jrha/2550N/src/jubilee.sch

## KiCad design src/jubilee.sch (2017-06-12)

Schematic: jubilee.sch

Parts:
C1: 0.047uF
C2, C4, C10, C21, C22, C23: 0.1uF
C3: 0.68uF
C5, C20: 47pF
C6: 0.0047uF
C7: 0.01uF
C8, C11, C18, C26, C30, C31: 50uF 500V
C9, C17: 0.001uF
C12: 220pF
C13, C14: 470pF
C15, C33, C34: 10uF
C16, C19, C24, C25: 0.022uF
C27: 0.0022uF
C28: 22uF
C29: 470uF
C32: 0.002uF
C35: 0.033uF
D1, D2, D3, D4, D6, D7, D9, D11, D12, D13, D14, D15: 1N4007
D5, D8: Red LED 1.8Vf 20mA
D10: LED
F1: 2A SloBlo
F2: 500mA
J1: Input
J2: FX Recv
J3: FX Send
J4: Footswitch
J5, J6: Speaker
JP1, JP2: JUMPER
K1: RELAY_DPDT
K2: Mains
L1: 3-5H 100R
P1, P2, P3, P4, P5, P6, P7, P8, P11, P12, P13: CONN_1
R1, R2, R20, R26, R40: 1M
R3, R23: 470R
R4: 68K
R5, R12, R16, R30, R31, R49: 220K
R6: 2.7K
R7, R8, R9, R11, R14, R15, R25, R27, R39, R42, R50: 100K
R10, R24, R28, R37: 10K
R13, R22: 1.5K
R17, R19, R41: 47K
R18, R32, R38: 10K 2W
R21: 82K
R29: 10R
R33, R34: 5.6K
R35, R36: 330R
R43, R44: 1R
R45, R46: 1K 5W
R47: 15K
R48: 56K
RV1, RV2, RV3, RV7: 1M Log
RV4: 100K Log
RV5, RV8: 220K Lin
RV9: 5K 2W Lin
RV10: 25K Lin
SW1, SW2: DPST
SW3: Rhythm Clip
SW4: SW_DPDT_x2
SW5: SW_SP3T
SW6: Channel
T1: 3.2K C.T. 50W
T1A1: 345-0-345V 150mA
T1B1: 6.3V C.T. 5A
V1, V2, V3: ECC83; VALVE-NOVAL_P
V4, V5: EL34; VALVE-OCTAL
W1, W2, W3, W4, W5, W6: Jumper

Notes on the sheet:
Hammond 1750N
Treble
Bass
Mid
Master Volume
Presence
Lead Volume
Clean Gain
Lead Gain
Dual Ganged Pot
Triode
Pentode
Loop Recovery
Power Amp
DPDT
Phase Inverter
Tone Stack
Master Volume
Shielded
Mounted on socket
Red
White
Blue
Violet
Orange
Yellow
Black
